ErezBorenshtein/Rubiks-clock-solver/Solid parts/clock_model/thumbnail.png

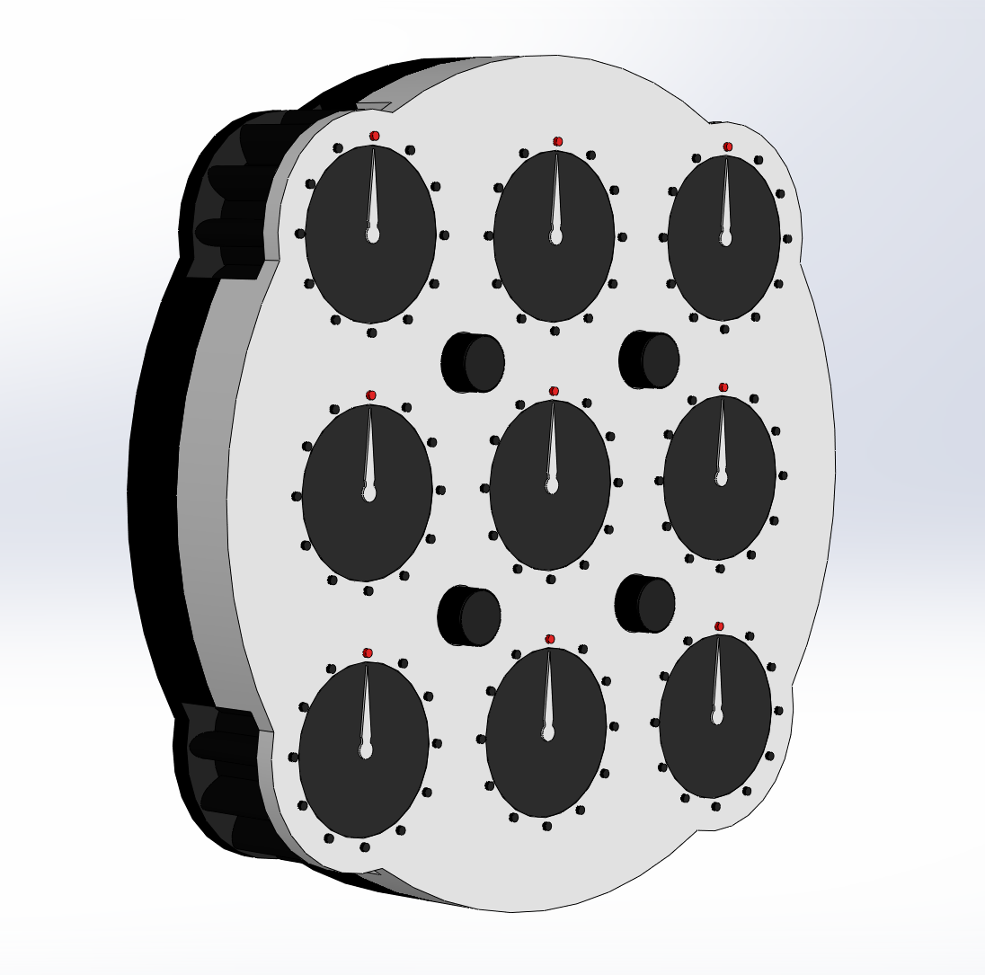
Solid parts/clock_model/thumbnail.png
