ErezBorenshtein/Rubiks-clock-solver/Solid parts/clock_model/full pin.SLDASM

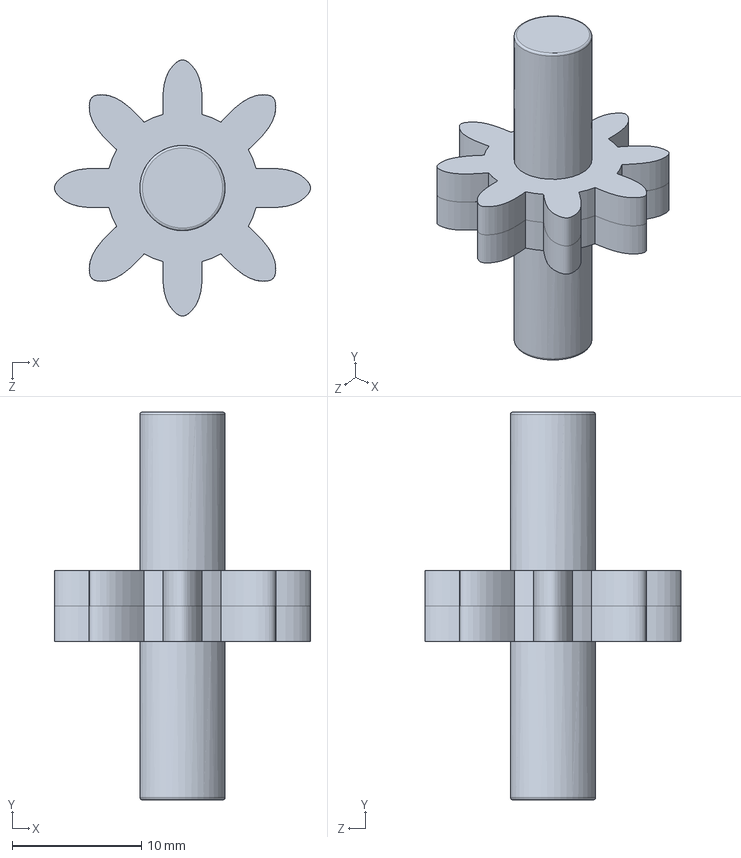
[picture p12: CAD file, 2024-03-16]
Solid parts/clock_model/full pin.SLDASM
19.8 x 30.0 x 19.8 mm
half_pin x 2
