ErezBorenshtein/Rubiks-clock-solver/Solid parts/limt switch/Wheel shaft.SLDPRT

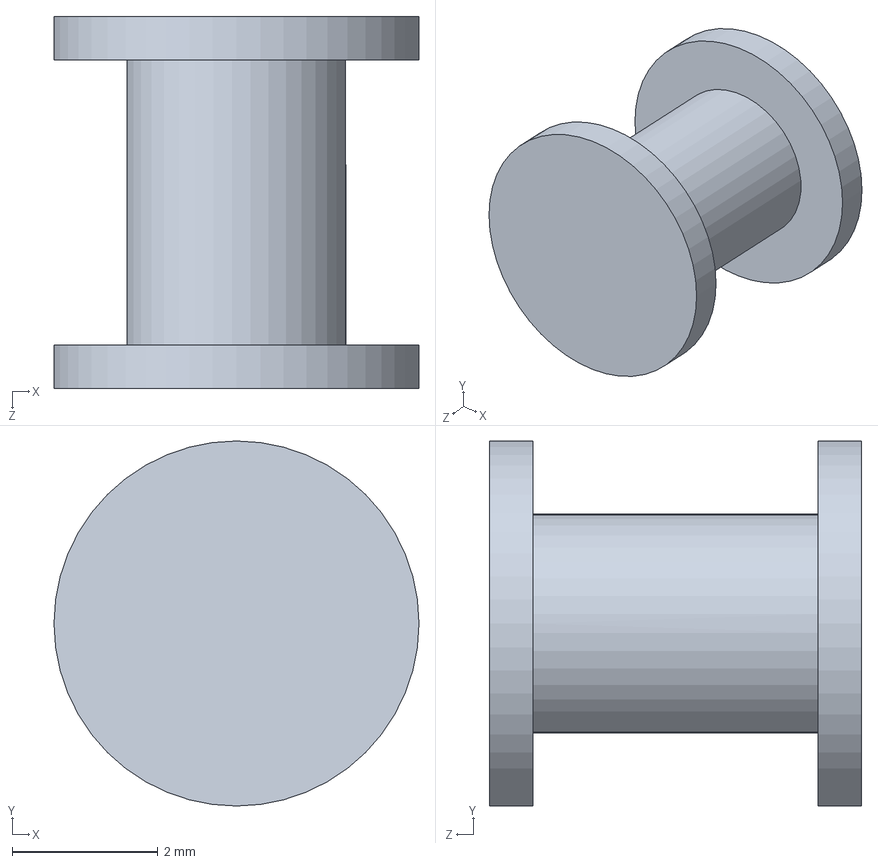
[picture p23: CAD file, 2024-05-01]
Solid parts/limt switch/Wheel shaft.SLDPRT
5.00 x 5.00 x 5.10 mm
