ErezBorenshtein/Rubiks-clock-solver/Stl parts/led_matrix_case.STL

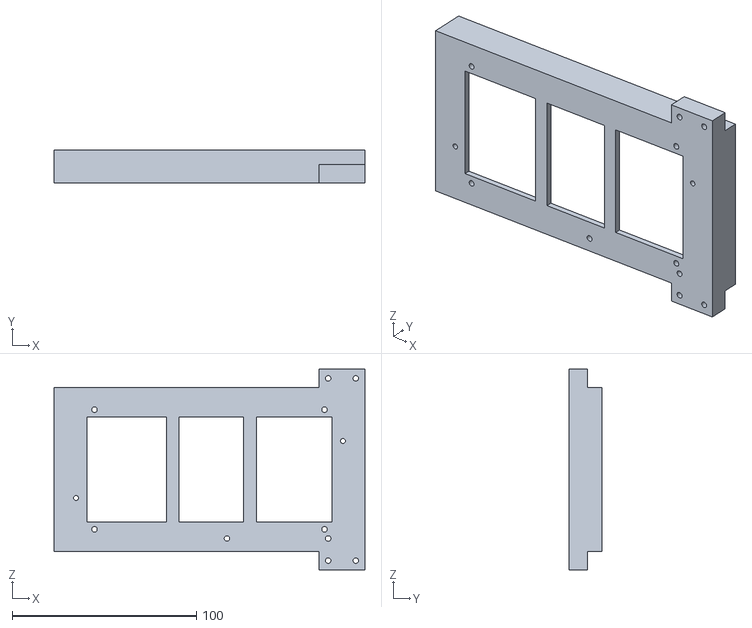
[picture p24: CAD file, 2024-07-09]
Stl parts/led_matrix_case.STL
169.0 x 18.0 x 109.0
