ErezBorenshtein/Rubiks-clock-solver/Solid parts/clock_model/transparent_layer.SLDPRT

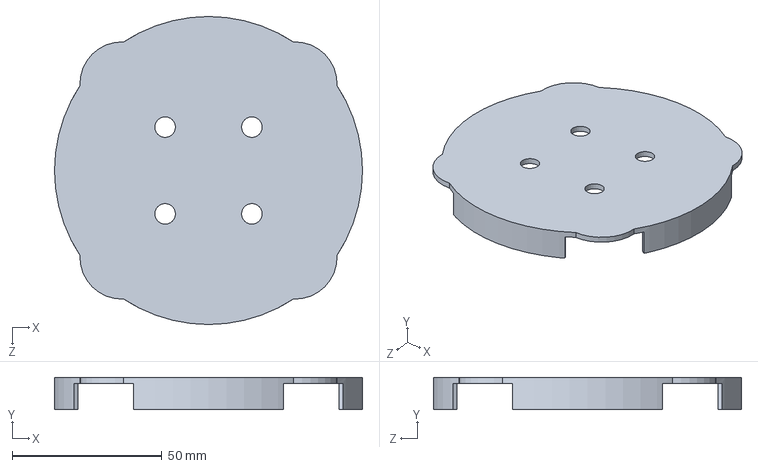
[picture p25: CAD file, 2024-03-16]
Solid parts/clock_model/transparent_layer.SLDPRT
103.0 x 10.8 x 103.0 mm
