ErezBorenshtein/Rubiks-clock-solver/Solid parts/limt switch/Link.SLDPRT

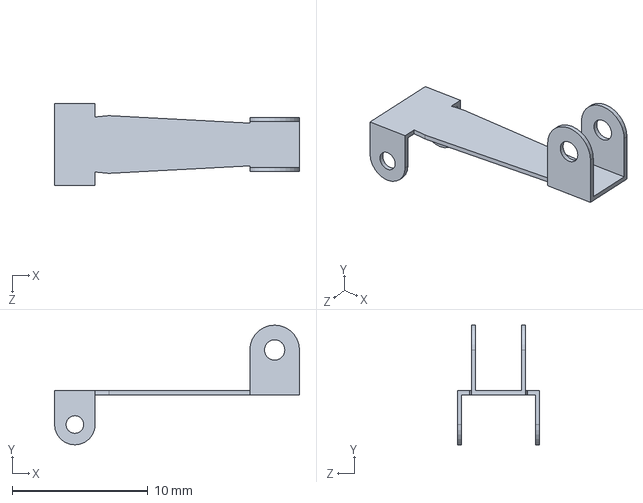
[picture p26: CAD file, 2024-05-01]
Solid parts/limt switch/Link.SLDPRT
18.0 x 8.82 x 6.05 mm
