ErezBorenshtein/Rubiks-clock-solver/Solid parts/limt switch/Wheel.SLDPRT

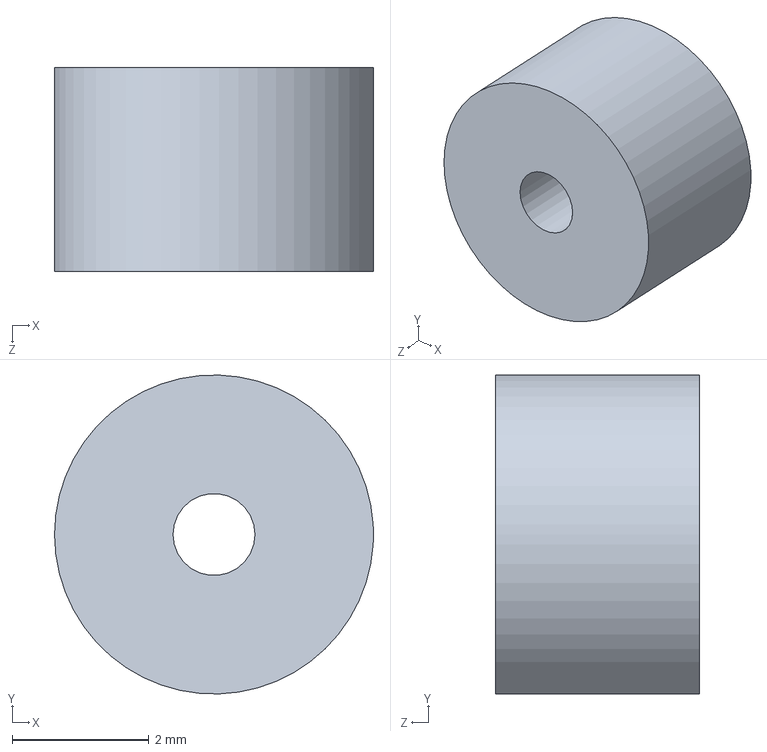
[picture p27: CAD file, 2024-05-01]
Solid parts/limt switch/Wheel.SLDPRT
4.67 x 4.67 x 2.99 mm
