ErezBorenshtein/Rubiks-clock-solver/Stl parts/Stepper wheel large._v2.STL

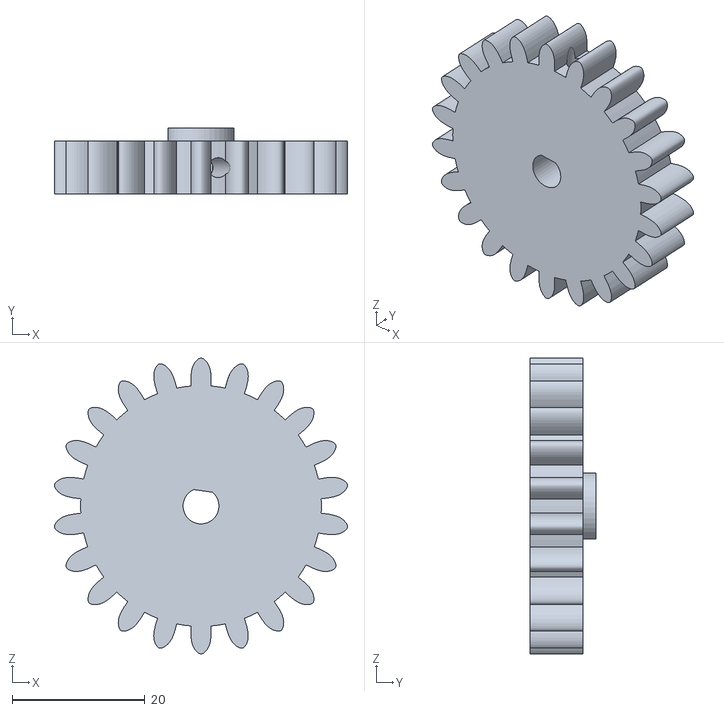
[picture p28: CAD file, 2024-06-28]
Stl parts/Stepper wheel large._v2.STL
44.2 x 10.0 x 44.6
