ErezBorenshtein/Rubiks-clock-solver/Solid parts/clock_model/cover_black.SLDPRT

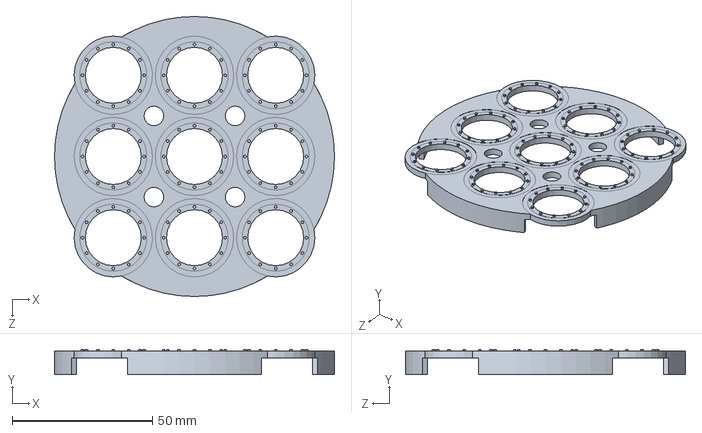
[picture p29: CAD file, 2024-03-16]
Solid parts/clock_model/cover_black.SLDPRT
100.0 x 9.00 x 100.0 mm
