ErezBorenshtein/Rubiks-clock-solver/Stl parts/Camera_base_2.STL

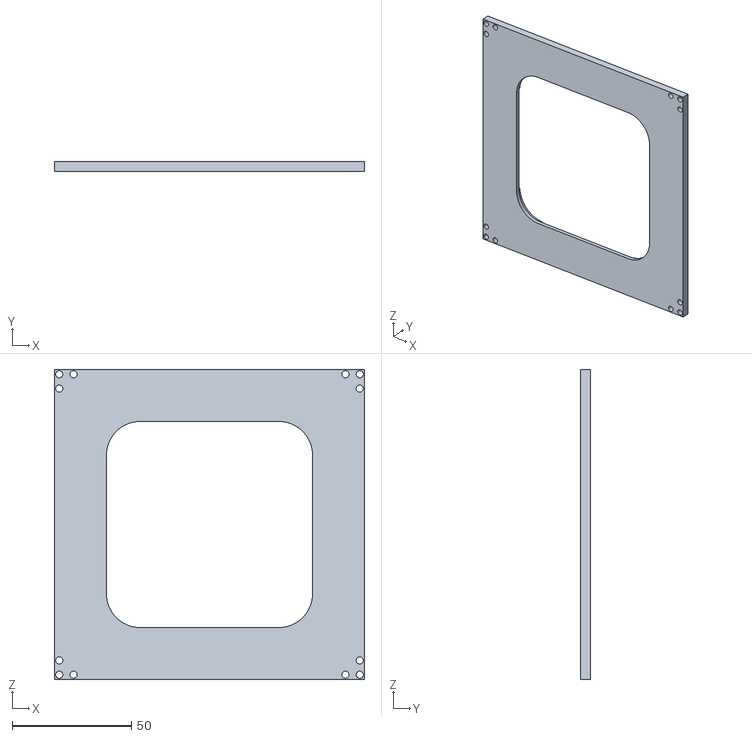
[picture p30: CAD file, 2024-06-22]
Stl parts/Camera_base_2.STL
130.0 x 4.00 x 130.0
