ErezBorenshtein/Rubiks-clock-solver/Solid parts/clock_model/half_pin.SLDPRT

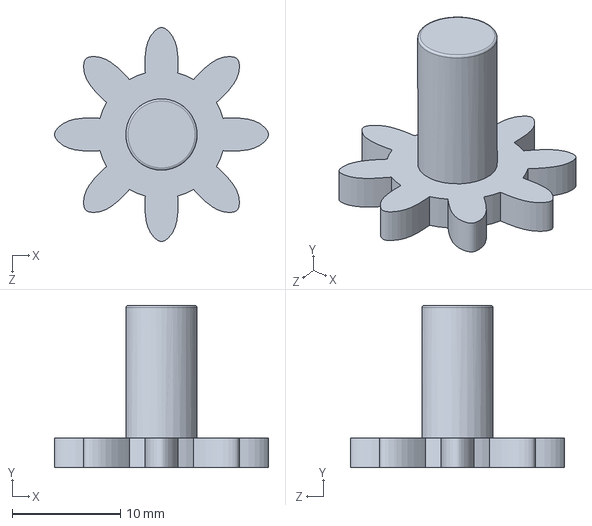
[picture p31: CAD file, 2024-03-16]
Solid parts/clock_model/half_pin.SLDPRT
19.8 x 15.0 x 19.8 mm
