ErezBorenshtein/Rubiks-clock-solver/Stl parts/Inner_spacer.STL

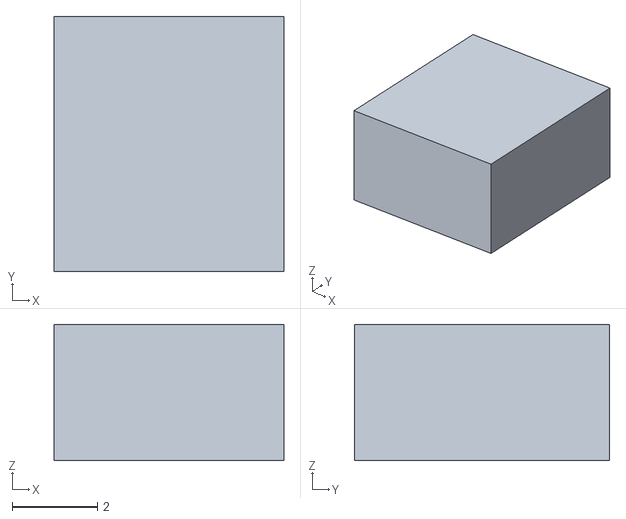
[picture p32: CAD file, 2024-06-22]
Stl parts/Inner_spacer.STL
5.40 x 6.00 x 3.20
