ErezBorenshtein/Rubiks-clock-solver/Stl parts/Stepper_gear_large.STL

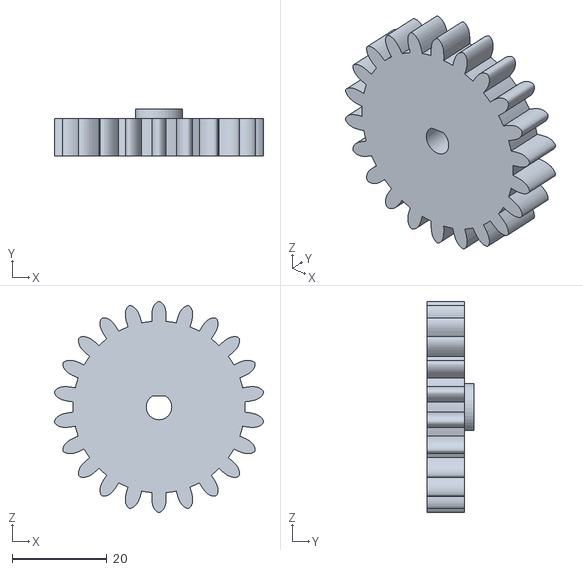
[picture p33: CAD file, 2024-06-22]
Stl parts/Stepper_gear_large.STL
44.2 x 10.0 x 44.6
