ErezBorenshtein/Rubiks-clock-solver/Solid parts/Stepper wheel.SLDPRT

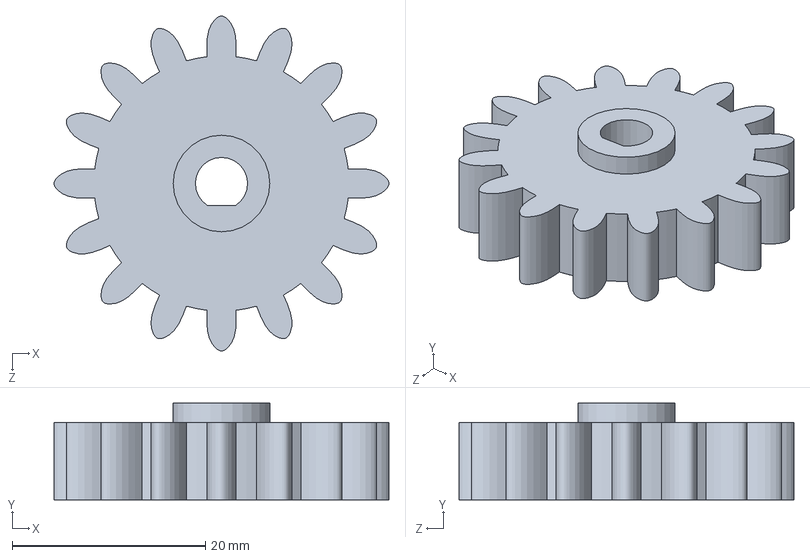
[picture p34: CAD file, 2024-06-22]
Solid parts/Stepper wheel.SLDPRT
34.7 x 10.0 x 34.7 mm
