ErezBorenshtein/Rubiks-clock-solver/Stl parts/T holder.STL

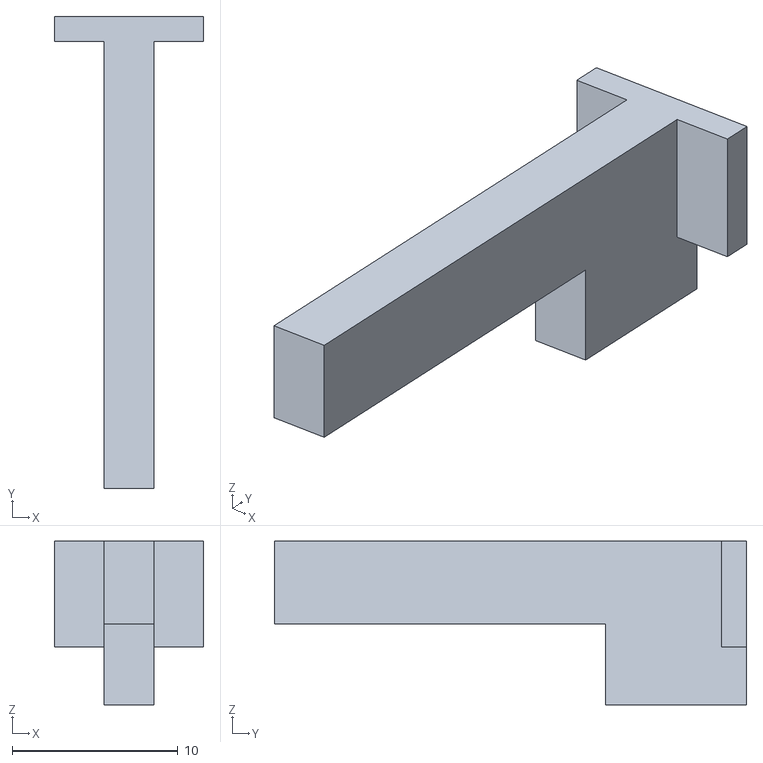
[picture p35: CAD file, 2024-06-22]
Stl parts/T holder.STL
9.00 x 28.5 x 9.90
