ErezBorenshtein/Rubiks-clock-solver/Solid parts/machine_holder.SLDPRT

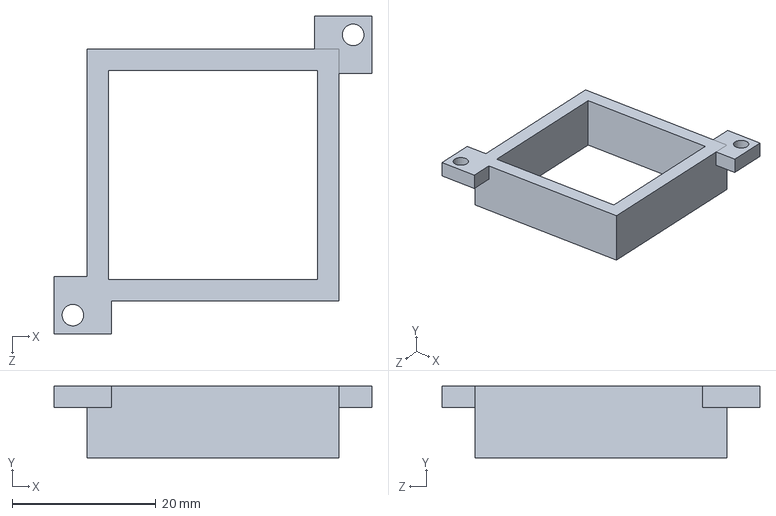
[picture p36: CAD file, 2024-06-22]
Solid parts/machine_holder.SLDPRT
44.2 x 10.0 x 44.2 mm
