ErezBorenshtein/Rubiks-clock-solver/Stl parts/limit_switch_mount.STL

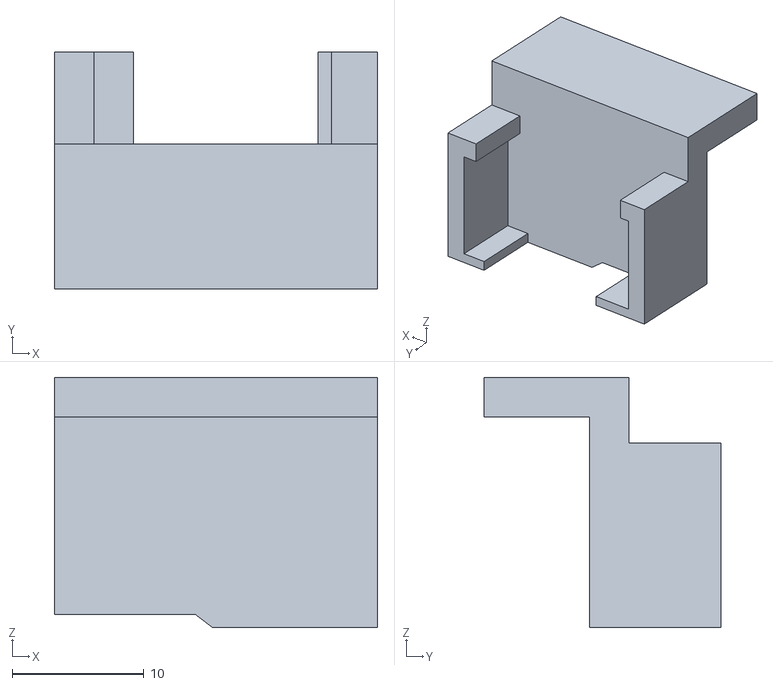
[picture p37: CAD file, 2024-06-22]
Stl parts/limit_switch_mount.STL
24.5 x 18.0 x 19.0
