ErezBorenshtein/Rubiks-clock-solver/Solid parts/17HM19-1684S.STEP

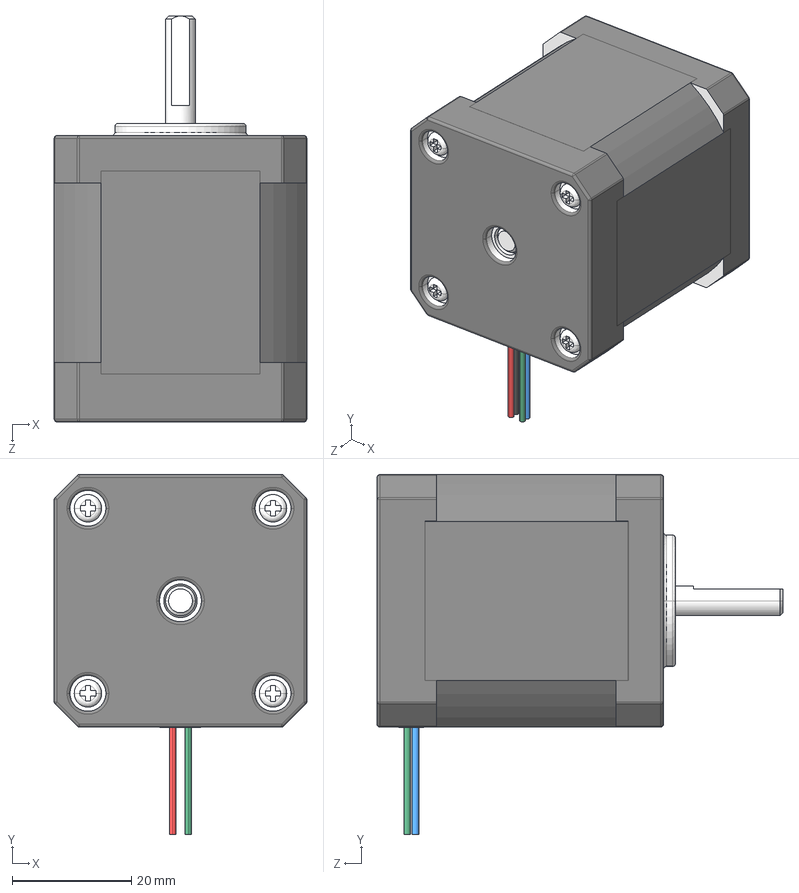
[picture p38: CAD file, 2024-06-22]
Solid parts/17HM19-1684S.STEP
42.3 x 60.3 x 68.0 mm
