ErezBorenshtein/Rubiks-clock-solver/Stl parts/solenoid_mount.STL

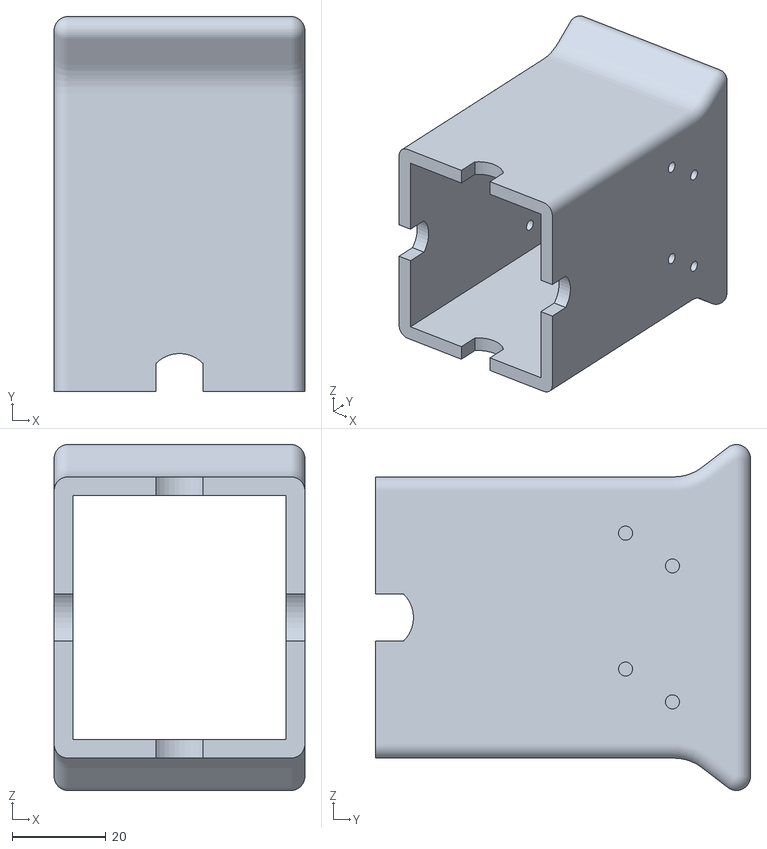
[picture p39: CAD file, 2024-04-21]
Stl parts/solenoid_mount.STL
53.5 x 80.0 x 73.8
