ErezBorenshtein/Rubiks-clock-solver/Stl parts/Brige_to_stick_connector.STL

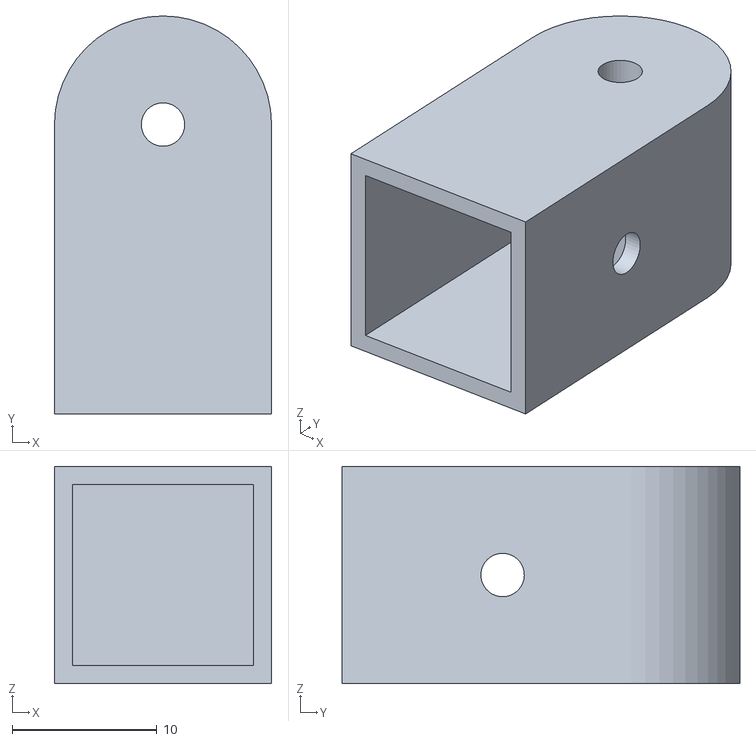
[picture p40: CAD file, 2024-03-16]
Stl parts/Brige_to_stick_connector.STL
15.0 x 27.5 x 15.0
