ErezBorenshtein/Rubiks-clock-solver/Stl parts/Base.STL

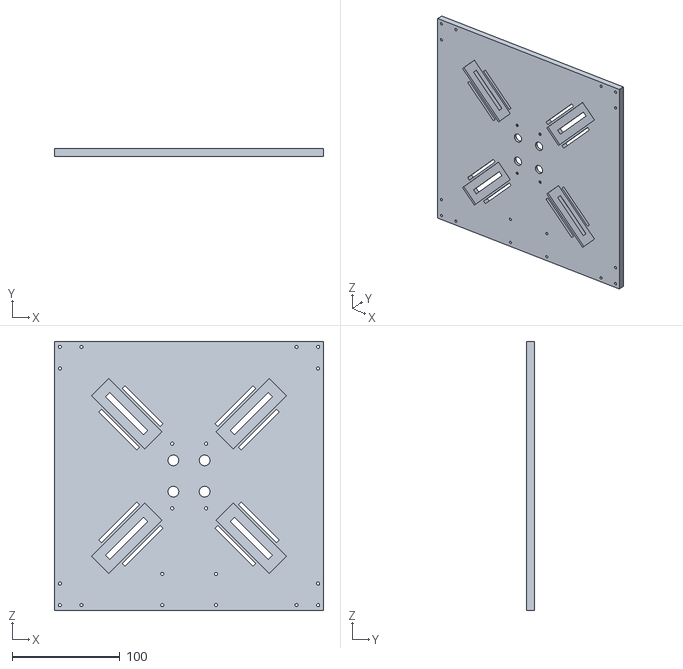
[picture p41: CAD file, 2024-03-16]
Stl parts/Base.STL
250.0 x 7.00 x 250.0
