ErezBorenshtein/Rubiks-clock-solver/Stl parts/Bridge_base.STL

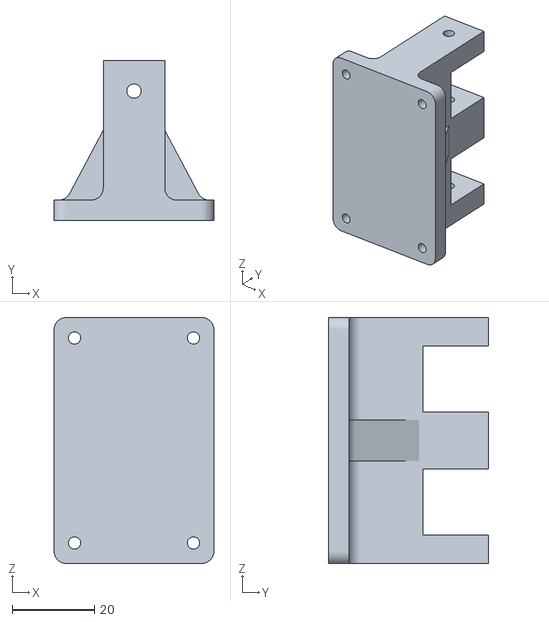
[picture p42: CAD file, 2024-03-16]
Stl parts/Bridge_base.STL
39.0 x 39.1 x 60.0
