ErezBorenshtein/Rubiks-clock-solver/Solid parts/legs.SLDPRT

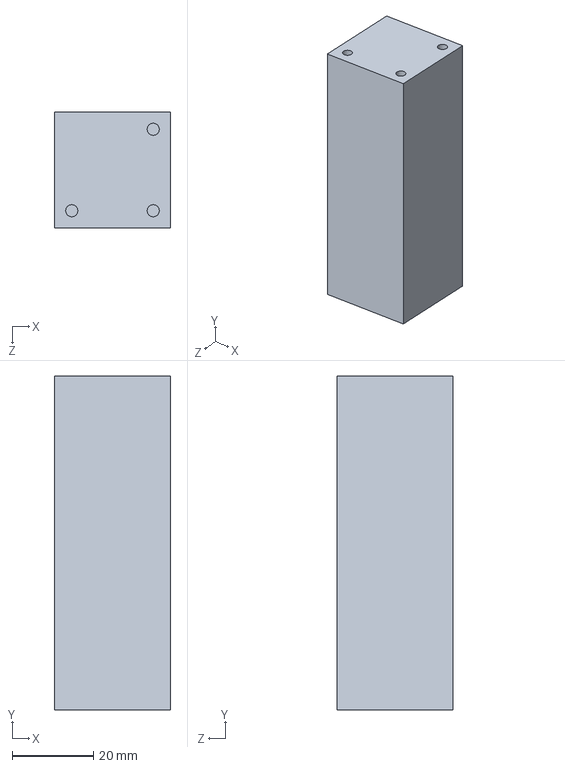
[picture p43: CAD file, 2024-06-14]
Solid parts/legs.SLDPRT
28.5 x 82.0 x 28.5 mm
