ErezBorenshtein/Rubiks-clock-solver/Solid parts/machine_base.SLDPRT

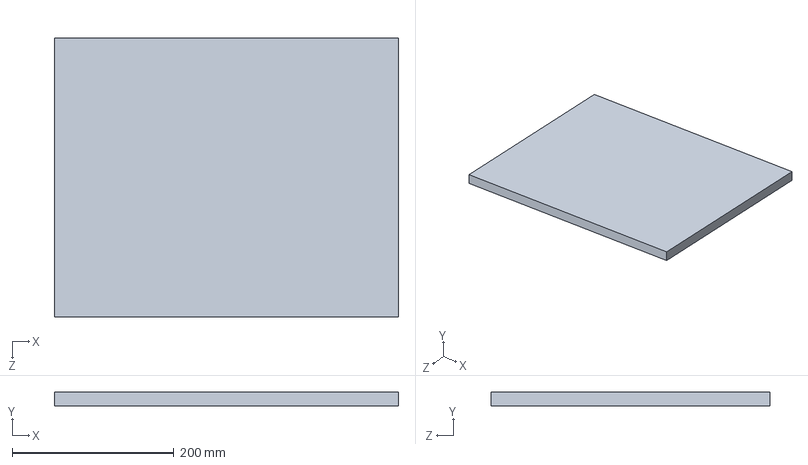
[picture p44: CAD file, 2024-03-16]
Solid parts/machine_base.SLDPRT
425.0 x 17.0 x 345.0 mm
