ErezBorenshtein/Rubiks-clock-solver/Solid parts/pusher_cap.SLDPRT

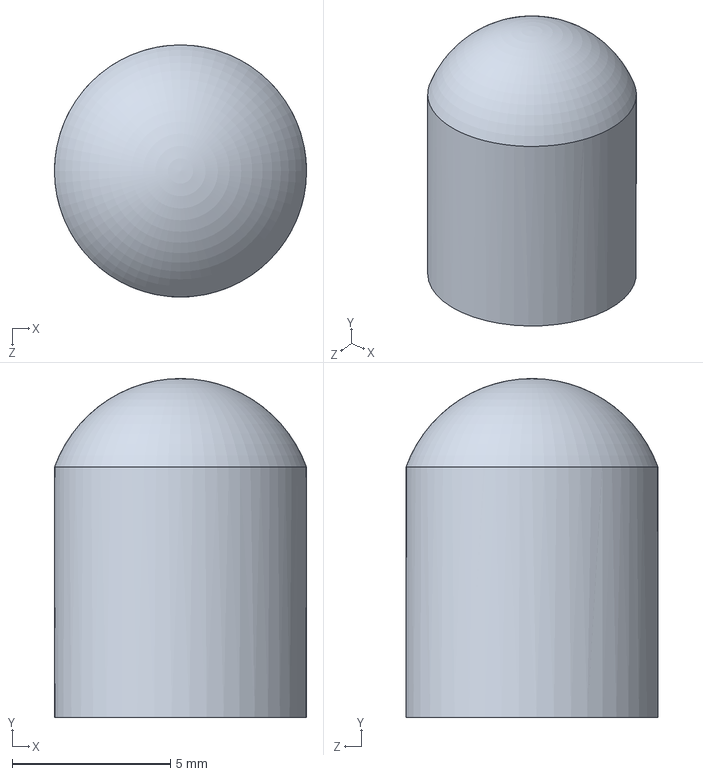
[picture p45: CAD file, 2024-03-16]
Solid parts/pusher_cap.SLDPRT
7.97 x 10.7 x 7.97 mm
