ErezBorenshtein/Rubiks-clock-solver/Solid parts/brige_part_2.SLDPRT

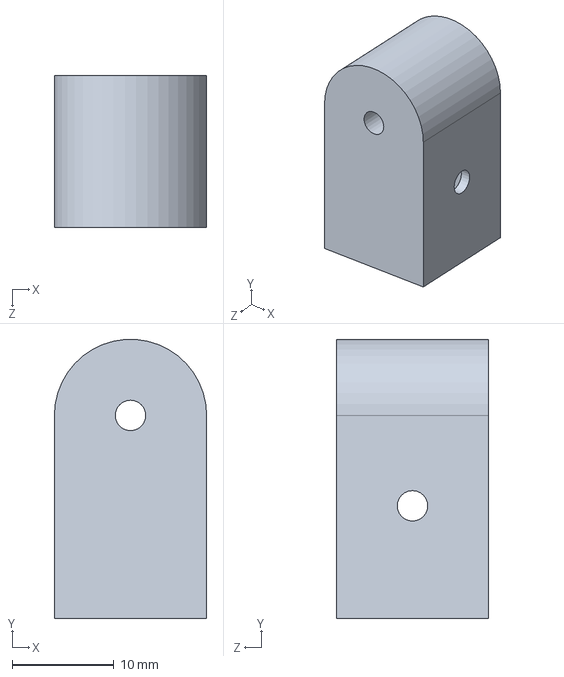
[picture p46: CAD file, 2024-03-16]
Solid parts/brige_part_2.SLDPRT
15.0 x 27.5 x 15.0 mm
