ErezBorenshtein/Rubiks-clock-solver/Solid parts/User Library-JF-0520B.sldprt

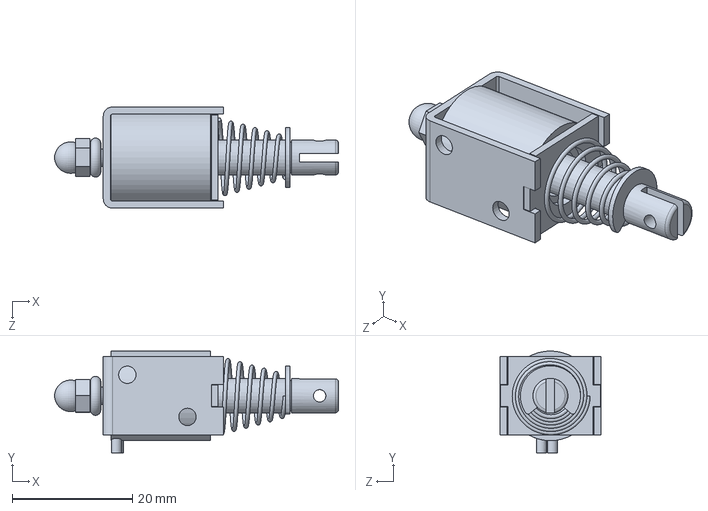
[picture p47: CAD file, 2024-03-16]
Solid parts/User Library-JF-0520B.sldprt
47.2 x 16.9 x 16.8 mm
