ErezBorenshtein/Rubiks-clock-solver/Code/arduino_code/RGB_led_matrix/my_font.h

// Created by https://oleddisplay.squix.ch/ Consider a donation
// In case of problems make sure that you are using the font file with the correct version!
const uint8_t DSEG7_Modern_Bold_16Bitmaps[] PROGMEM = {

	// Bitmap Data:
	0x00, // ' '
	0x00, // '!'
	0xFA,0x28,0xA2,0x8A,0x28,0xA2,0x8A,0x2F,0x80, // '"'
	0xFA,0x28,0xA2,0x8A,0x28,0xA2,0x8A,0x2F,0x80, // '#'
	0xFA,0x28,0xA2,0x8A,0x28,0xA2,0x8A,0x2F,0x80, // '$'
	0xFA,0x28,0xA2,0x8A,0x28,0xA2,0x8A,0x2F,0x80, // '%'
	0xFA,0x28,0xA2,0x8A,0x28,0xA2,0x8A,0x2F,0x80, // '&'
	0xFA,0x28,0xA2,0x8A,0x28,0xA2,0x8A,0x2F,0x80, // '''
	0xFA,0x28,0xA2,0x8A,0x28,0xA2,0x8A,0x2F,0x80, // '('
	0xFA,0x28,0xA2,0x8A,0x28,0xA2,0x8A,0x2F,0x80, // ')'
	0xFA,0x28,0xA2,0x8A,0x28,0xA2,0x8A,0x2F,0x80, // '*'
	0xFA,0x28,0xA2,0x8A,0x28,0xA2,0x8A,0x2F,0x80, // '+'
	0xFA,0x28,0xA2,0x8A,0x28,0xA2,0x8A,0x2F,0x80, // ','
	0x7E,0xFC, // '-'
	0xD8, // '.'
	0xFA,0x28,0xA2,0x8A,0x28,0xA2,0x8A,0x2F,0x80, // '/'
	0xFF,0x3F,0xEC,0x0B,0x06,0xC1,0xB0,0x6C,0x1A,0x00,0x00,0xB0,0x6C,0x1B,0x06,0xC1,0xA0,0x6F,0xF9,0xFE, // '0'
	0x09,0x6D,0xB0,0x5B,0x6D,0x90, // '1'
	0xFF,0x1F,0xE0,0x08,0x06,0x01,0x80,0x60,0x18,0xFC,0x7E,0x30,0x0C,0x03,0x00,0xC0,0x20,0x0F,0xF1,0xFE, // '2'
	0xFF,0x1F,0xE0,0x08,0x06,0x01,0x80,0x60,0x18,0xFC,0x7E,0x80,0x60,0x18,0x06,0x01,0x80,0x67,0xF9,0xFE, // '3'
	0x00,0x20,0x2C,0x0B,0x06,0xC1,0xB0,0x6C,0x1A,0xFC,0x7E,0x80,0x60,0x18,0x06,0x01,0x80,0x60,0x08, // '4'
	0xFF,0x3F,0xCC,0x03,0x00,0xC0,0x30,0x0C,0x02,0xFC,0x7E,0x80,0x60,0x18,0x06,0x01,0x80,0x67,0xF9,0xFE, // '5'
	0xFF,0x3F,0xCC,0x03,0x00,0xC0,0x30,0x0C,0x02,0xFC,0x7E,0xB0,0x6C,0x1B,0x06,0xC1,0xA0,0x6F,0xF9,0xFE, // '6'
	0xFF,0x3F,0xEC,0x0B,0x06,0xC1,0xB0,0x6C,0x1A,0x00,0x00,0x80,0x60,0x18,0x06,0x01,0x80,0x60,0x08, // '7'
	0xFF,0x3F,0xEC,0x0B,0x06,0xC1,0xB0,0x6C,0x1A,0xFC,0x7E,0xB0,0x6C,0x1B,0x06,0xC1,0xA0,0x6F,0xF9,0xFE, // '8'
	0xFF,0x3F,0xEC,0x0B,0x06,0xC1,0xB0,0x6C,0x1A,0xFC,0x7E,0x80,0x60,0x18,0x06,0x01,0x80,0x67,0xF9,0xFE, // '9'
	0xD0,0x00,0x06,0x00, // ':'
	0xFA,0x28,0xA2,0x8A,0x28,0xA2,0x8A,0x2F,0x80, // ';'
	0xFA,0x28,0xA2,0x8A,0x28,0xA2,0x8A,0x2F,0x80, // '<'
	0xFA,0x28,0xA2,0x8A,0x28,0xA2,0x8A,0x2F,0x80, // '='
	0xFA,0x28,0xA2,0x8A,0x28,0xA2,0x8A,0x2F,0x80, // '>'
	0xFA,0x28,0xA2,0x8A,0x28,0xA2,0x8A,0x2F,0x80, // '?'
	0xFA,0x28,0xA2,0x8A,0x28,0xA2,0x8A,0x2F,0x80, // '@'
	0xFF,0x3F,0xEC,0x0B,0x06,0xC1,0xB0,0x6C,0x1A,0xFC,0x7E,0xB0,0x6C,0x1B,0x06,0xC1,0xA0,0x68,0x08,0x00, // 'A'
	0x80,0x30,0x0C,0x03,0x00,0xC0,0x30,0x0B,0xF1,0xFA,0xC1,0xB0,0x6C,0x1B,0x06,0x81,0xBF,0xE7,0xF8, // 'B'
	0x3F,0x1F,0x8C,0x03,0x00,0xC0,0x30,0x08,0x03,0xFC,0x7F,0x80, // 'C'
	0x00,0x00,0x20,0x08,0x06,0x01,0x80,0x60,0x18,0xFC,0x7E,0xB0,0x6C,0x1B,0x06,0xC1,0xA0,0x6F,0xF9,0xFE, // 'D'
	0xFF,0x3F,0xCC,0x03,0x00,0xC0,0x30,0x0C,0x02,0xFC,0x7E,0x30,0x0C,0x03,0x00,0xC0,0x20,0x0F,0xF1,0xFE, // 'E'
	0xFF,0x3F,0xCC,0x03,0x00,0xC0,0x30,0x0C,0x02,0xFC,0x7E,0x30,0x0C,0x03,0x00,0xC0,0x20,0x08,0x00,0x00, // 'F'
	0xFF,0x3F,0xCC,0x03,0x00,0xC0,0x30,0x0C,0x02,0x00,0x00,0xB0,0x6C,0x1B,0x06,0xC1,0xA0,0x6F,0xF9,0xFE, // 'G'
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
};
const GFXglyph DSEG7_Modern_Bold_16Glyphs[] PROGMEM = {
// bitmapOffset, width, height, xAdvance, xOffset, yOffset
	  {     0,   2,   1,   4,    0,   -1 }, // ' '
	  {     1,   2,   1,  14,    0,   -1 }, // '!'
	  {     2,   6,  11,   7,    1,  -11 }, // '"'
	  {    11,   6,  11,   7,    1,  -11 }, // '#'
	  {    20,   6,  11,   7,    1,  -11 }, // '$'
	  {    29,   6,  11,   7,    1,  -11 }, // '%'
	  {    38,   6,  11,   7,    1,  -11 }, // '&'
	  {    47,   6,  11,   7,    1,  -11 }, // '''
	  {    56,   6,  11,   7,    1,  -11 }, // '('
	  {    65,   6,  11,   7,    1,  -11 }, // ')'
	  {    74,   6,  11,   7,    1,  -11 }, // '*'
	  {    83,   6,  11,   7,    1,  -11 }, // '+'
	  {    92,   6,  11,   7,    1,  -11 }, // ','
	  {   101,   8,   2,  14,    3,   -9 }, // '-'
	  {   103,   3,   2,   1,   -1,   -2 }, // '.'
	  {   104,   6,  11,   7,    1,  -11 }, // '/'
	  {   113,  10,  16,  14,    2,  -16 }, // '0'
	  {   133,   3,  15,  14,    9,  -16 }, // '1'
	  {   139,  10,  16,  14,    2,  -16 }, // '2'
	  {   159,  10,  16,  14,    2,  -16 }, // '3'
	  {   179,  10,  15,  14,    2,  -16 }, // '4'
	  {   198,  10,  16,  14,    2,  -16 }, // '5'
	  {   218,  10,  16,  14,    2,  -16 }, // '6'
	  {   238,  10,  15,  14,    2,  -16 }, // '7'
	  {   257,  10,  16,  14,    2,  -16 }, // '8'
	  {   277,  10,  16,  14,    2,  -16 }, // '9'
	  {   297,   3,   9,   4,    1,  -12 }, // ':'
	  {   301,   6,  11,   7,    1,  -11 }, // ';'
	  {   310,   6,  11,   7,    1,  -11 }, // '<'
	  {   319,   6,  11,   7,    1,  -11 }, // '='
	  {   328,   6,  11,   7,    1,  -11 }, // '>'
	  {   337,   6,  11,   7,    1,  -11 }, // '?'
	  {   346,   6,  11,   7,    1,  -11 }, // '@'
	  {   355,  10,  16,  14,    2,  -16 }, // 'A'
	  {   375,  10,  15,  14,    2,  -15 }, // 'B'
	  {   394,  10,   9,  14,    2,   -9 }, // 'C'
	  {   406,  10,  16,  14,    2,  -16 }, // 'D'
	  {   426,  10,  16,  14,    2,  -16 }, // 'E'
	  {   446,  10,  16,  14,    2,  -16 }, // 'F'
	  {   466,  10,  16,  14,    2,  -16 }, // 'G'
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
};
const GFXfont DSEG7_Modern_Bold_16 PROGMEM = {
(uint8_t  *)DSEG7_Modern_Bold_16Bitmaps,(GFXglyph *)DSEG7_Modern_Bold_16Glyphs,0x20, 0x7E, 18};
